johannesschlaf/phyphox_quantum_experiments/Measuring Planck's Constant/Instructions/typ-files/en/Figures/LED_cc_reduced.pdf

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

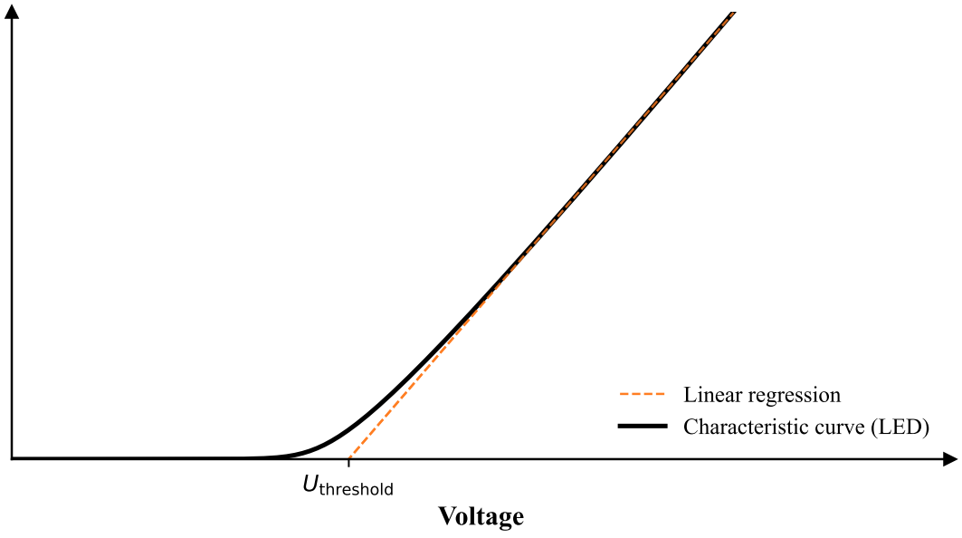
[picture p33: figure]
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
