johannesschlaf/phyphox_quantum_experiments/BB84 Analogy/Instructions/typ-files/de/Abbildungen/Screenshot_Alice.jpg

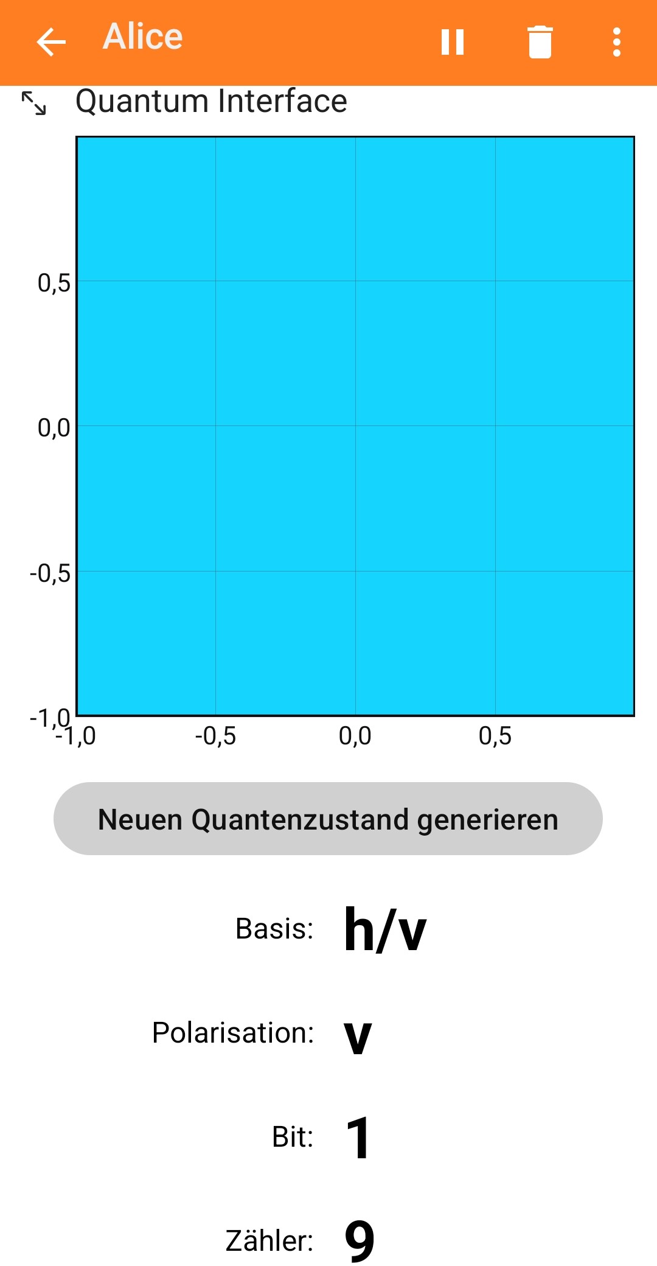
BB84 Analogy/Instructions/typ-files/de/Abbildungen/Screenshot_Alice.jpg
