johannesschlaf/phyphox_quantum_experiments/Measuring Planck's Constant/Instructions/typ-files/de/Abbildungen/Abb_Bau/3D-Druck/h-Oberseite.jpg

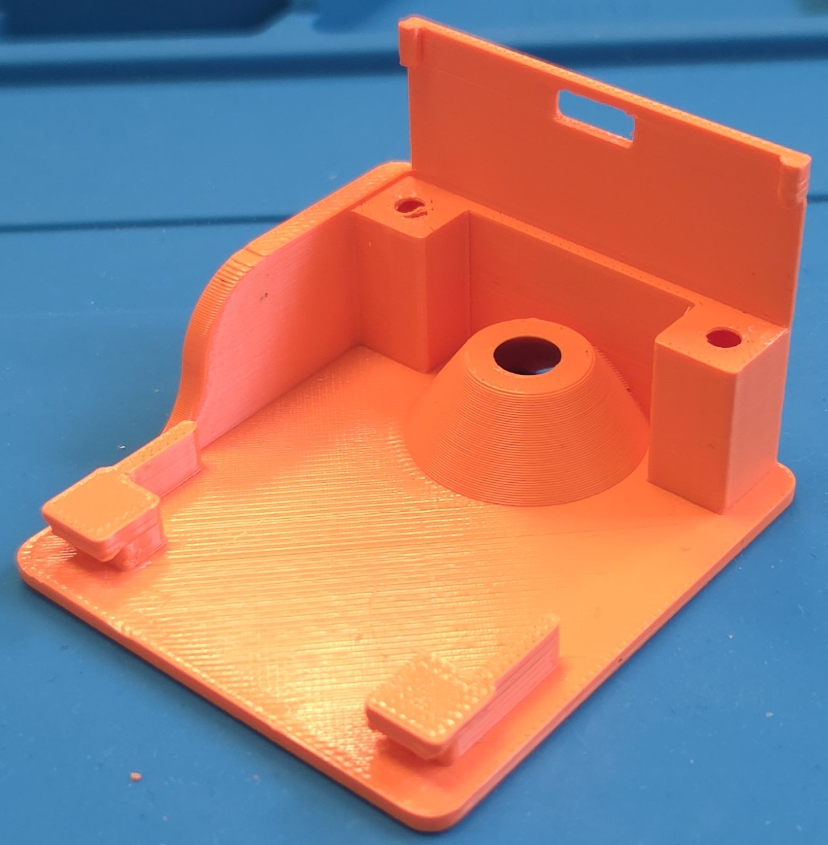
Measuring Planck's Constant/Instructions/typ-files/de/Abbildungen/Abb_Bau/3D-Druck/h-Oberseite.jpg
