johannesschlaf/phyphox_quantum_experiments/Measuring Planck's Constant/Instructions/typ-files/de/Abbildungen/Abb_Bau/LED-Einsatz/LED-Einsatz_1_markiert.jpg

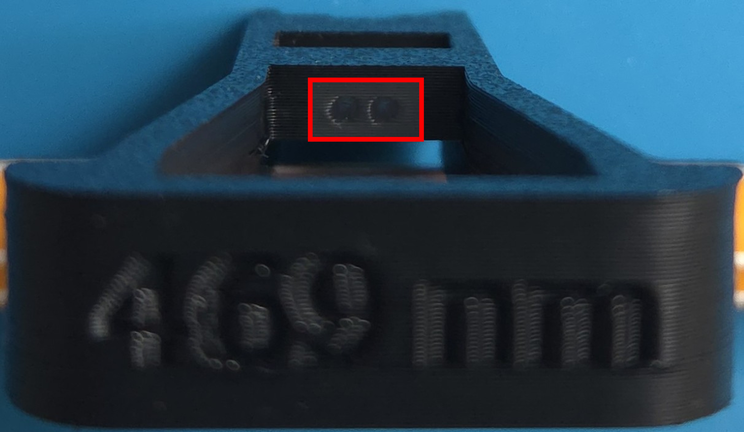
Measuring Planck's Constant/Instructions/typ-files/de/Abbildungen/Abb_Bau/LED-Einsatz/LED-Einsatz_1_markiert.jpg
