johannesschlaf/phyphox_quantum_experiments/Measuring Planck's Constant/Instructions/typ-files/de/Abbildungen/Abb_Bau/Loeten/Platine_Nasen_abgeschmirgelt.jpg

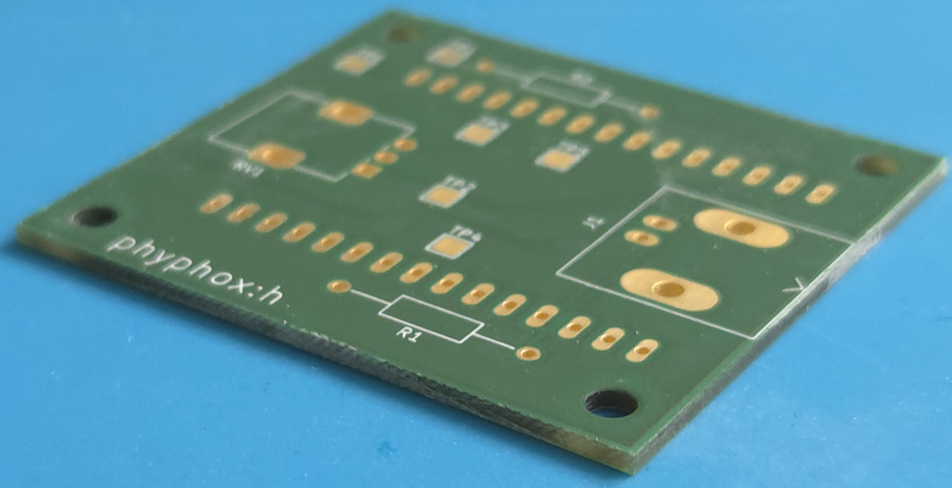
Measuring Planck's Constant/Instructions/typ-files/de/Abbildungen/Abb_Bau/Loeten/Platine_Nasen_abgeschmirgelt.jpg
