johannesschlaf/phyphox_quantum_experiments/Measuring Planck's Constant/Instructions/typ-files/de/Abbildungen/Abb_Bau/Nachbearbeitung/h-Oberseite_Stuetzstruktur.jpg

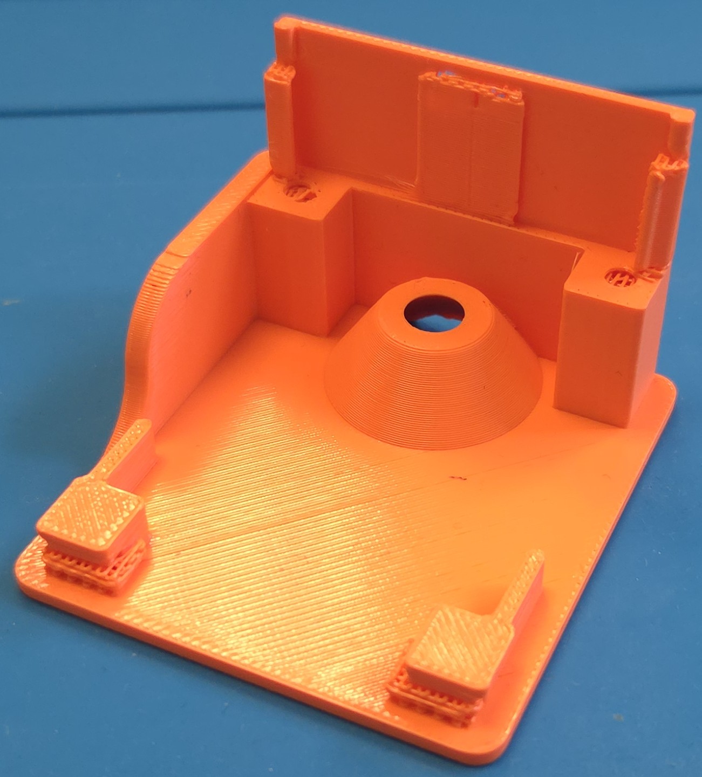
Measuring Planck's Constant/Instructions/typ-files/de/Abbildungen/Abb_Bau/Nachbearbeitung/h-Oberseite_Stuetzstruktur.jpg
