johannesschlaf/phyphox_quantum_experiments/Measuring Planck's Constant/Instructions/typ-files/de/Abbildungen/Abb_Bau/Programmierung/Arduino_IDE_Basic_markiert.png

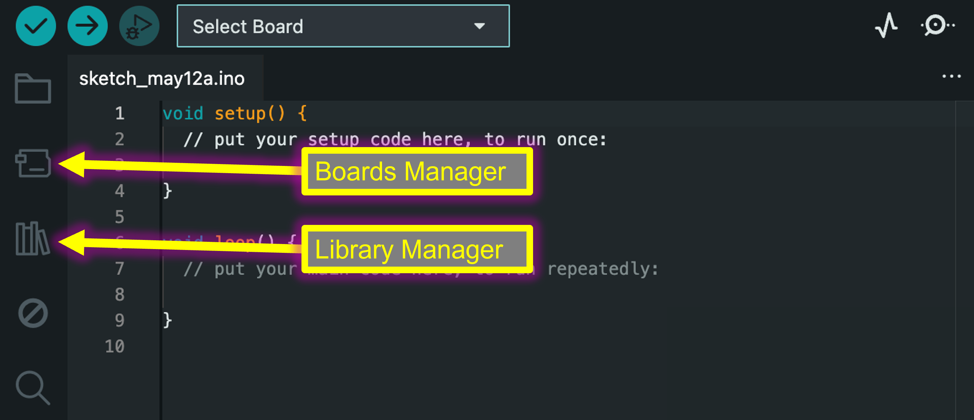
Measuring Planck's Constant/Instructions/typ-files/de/Abbildungen/Abb_Bau/Programmierung/Arduino_IDE_Basic_markiert.png
