johannesschlaf/phyphox_quantum_experiments/Measuring Planck's Constant/Instructions/typ-files/de/Abbildungen/Abb_Bau/Programmierung/Board.png

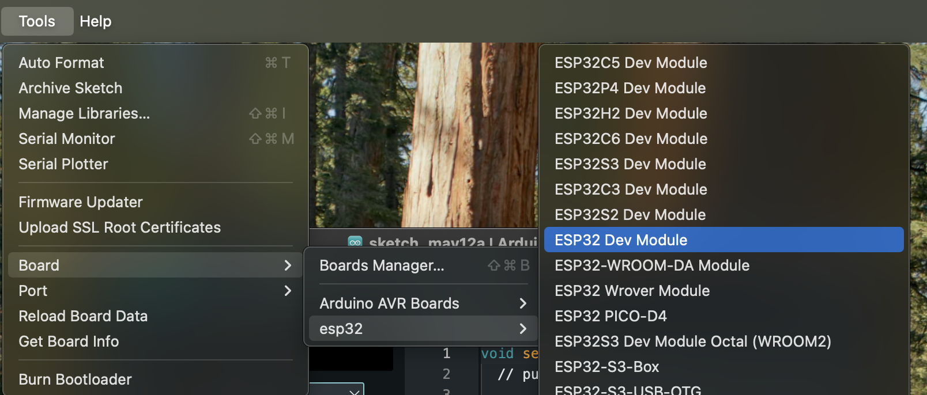
Measuring Planck's Constant/Instructions/typ-files/de/Abbildungen/Abb_Bau/Programmierung/Board.png
