johannesschlaf/phyphox_quantum_experiments/Measuring Planck's Constant/Instructions/typ-files/de/Abbildungen/Abb_Bau/Programmierung/Espressif_ESP32.png

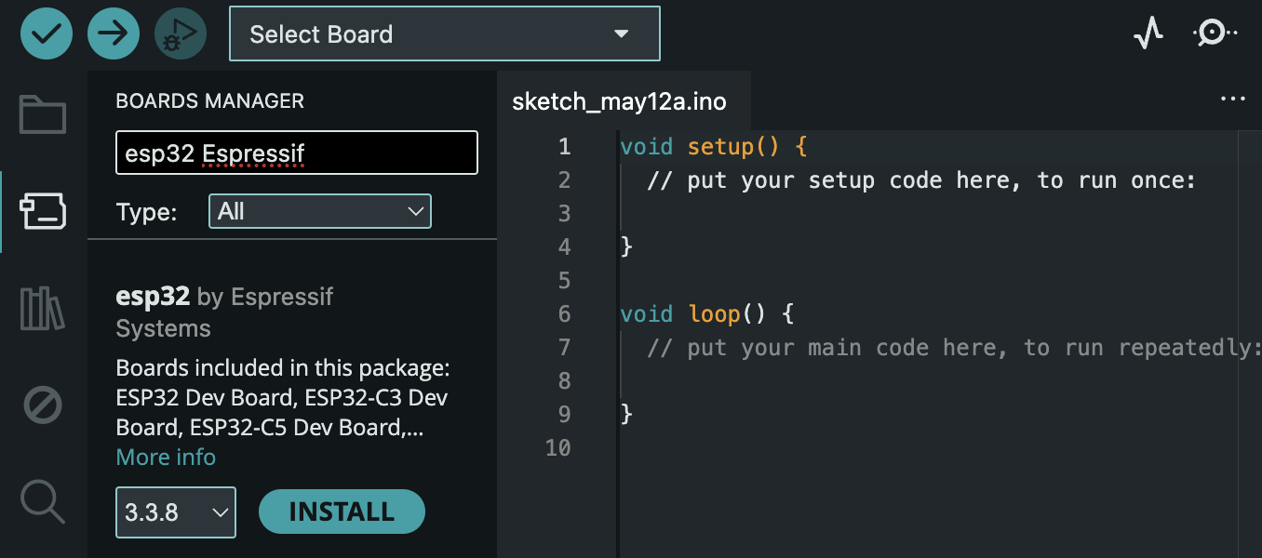
Measuring Planck's Constant/Instructions/typ-files/de/Abbildungen/Abb_Bau/Programmierung/Espressif_ESP32.png
