johannesschlaf/phyphox_quantum_experiments/Measuring Planck's Constant/Instructions/typ-files/de/Abbildungen/Abb_Bau/Programmierung/Espressif_ESP32_markiert.png

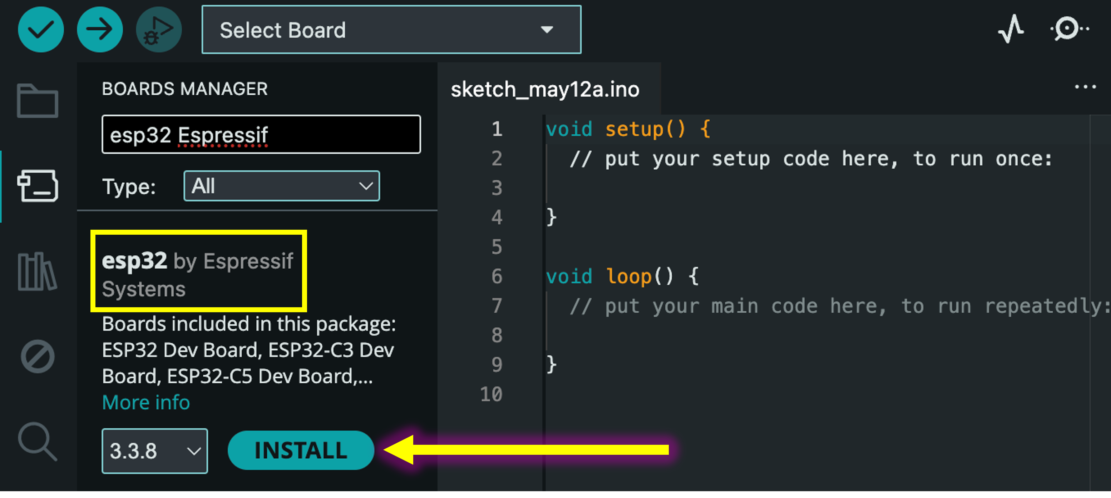
Measuring Planck's Constant/Instructions/typ-files/de/Abbildungen/Abb_Bau/Programmierung/Espressif_ESP32_markiert.png
