johannesschlaf/phyphox_quantum_experiments/Measuring Planck's Constant/Instructions/typ-files/en/Figures/EM_wave.pdf

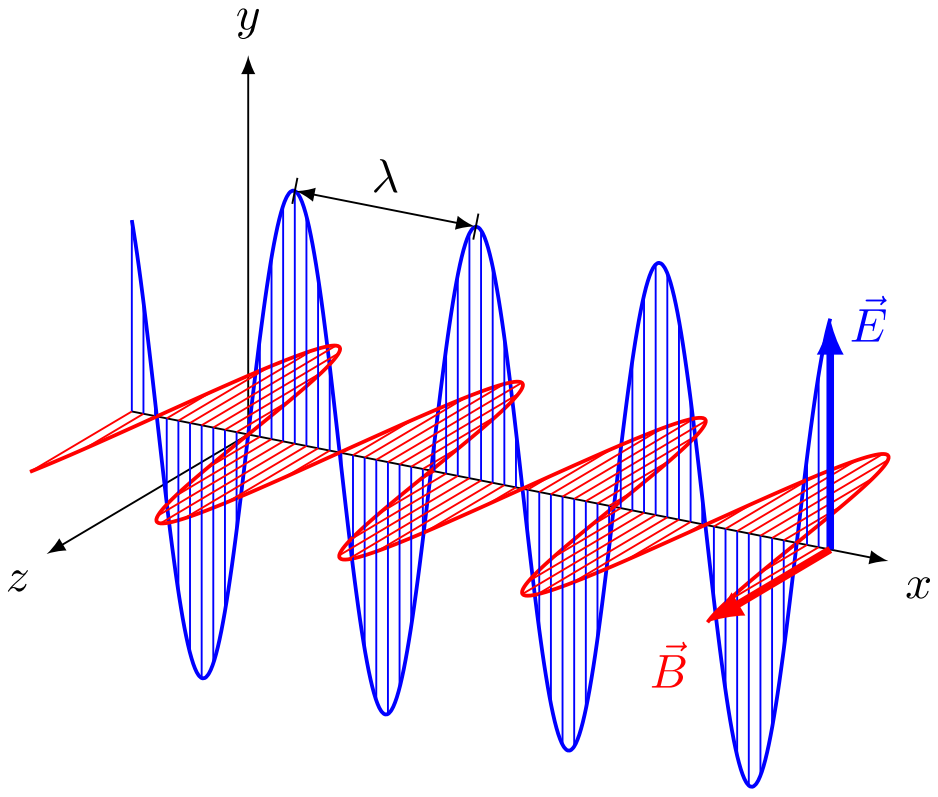
[picture p137: page 1]
