johannesschlaf/phyphox_quantum_experiments/BB84 Analogy/Instructions/typ-files/en/Grafiken/phyphox_bright_r.pdf

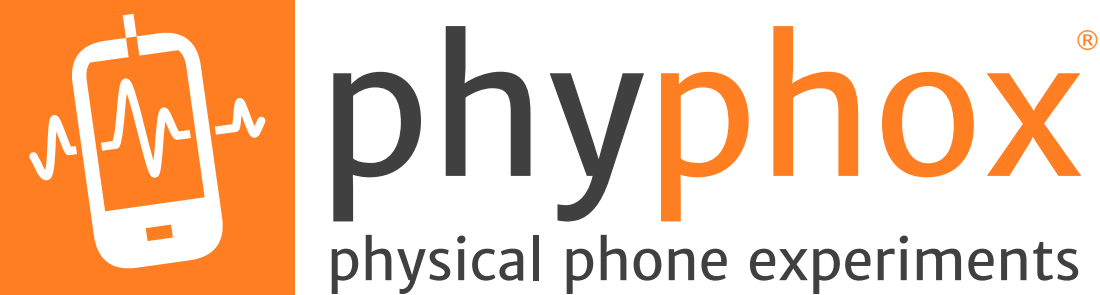
[picture p138: page 1]
