johannesschlaf/phyphox_quantum_experiments/BB84 Analogy/Instructions/typ-files/de/Abbildungen/BB84_komplett.pdf

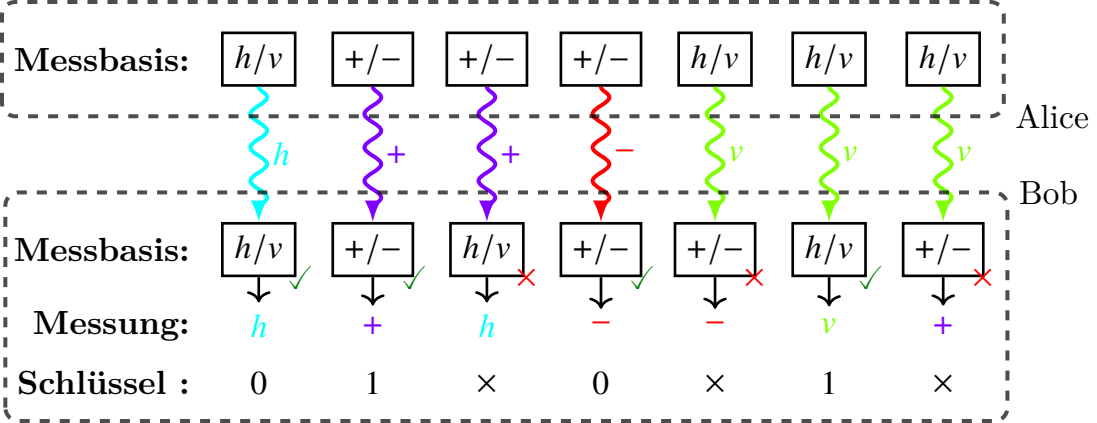
[picture p139: page 1]
Messbasis:; Messung: Schlüssel :; Alice; Bob
